blaketolmie/LFR/LFR Report LaTeX - Sections split up/JSON/example error  “LaTeX Workshop” and “vscode-pdf” clash.png

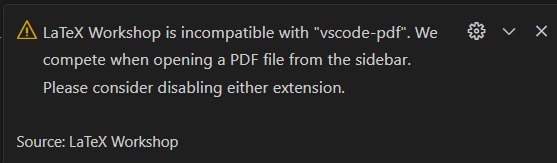
LFR Report LaTeX - Sections split up/JSON/example error “LaTeX Workshop” and “vscode-pdf” clash.png
