blaketolmie/LFR/LFR Report LaTeX - Sections split up/JSON/move pdf into new window.png

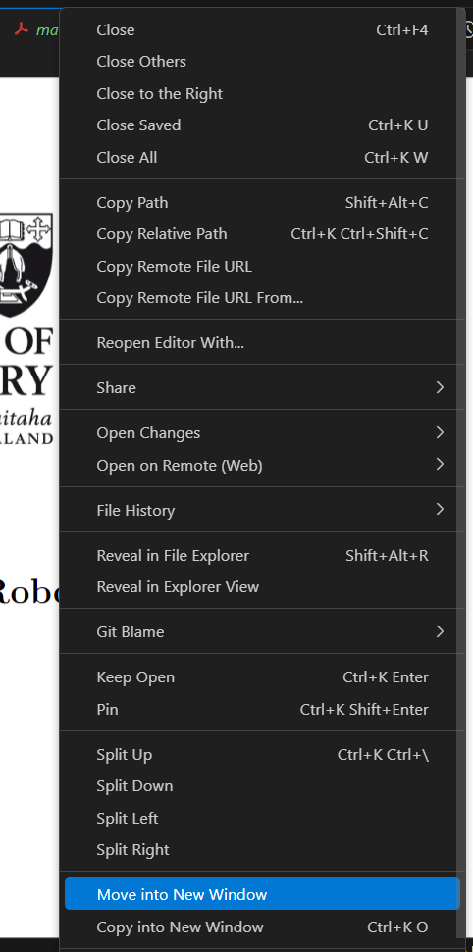
LFR Report LaTeX - Sections split up/JSON/move pdf into new window.png
