blaketolmie/LFR/LFR Report LaTeX - Sections split up/JSON/Opening JSON ctrl and ,  .png

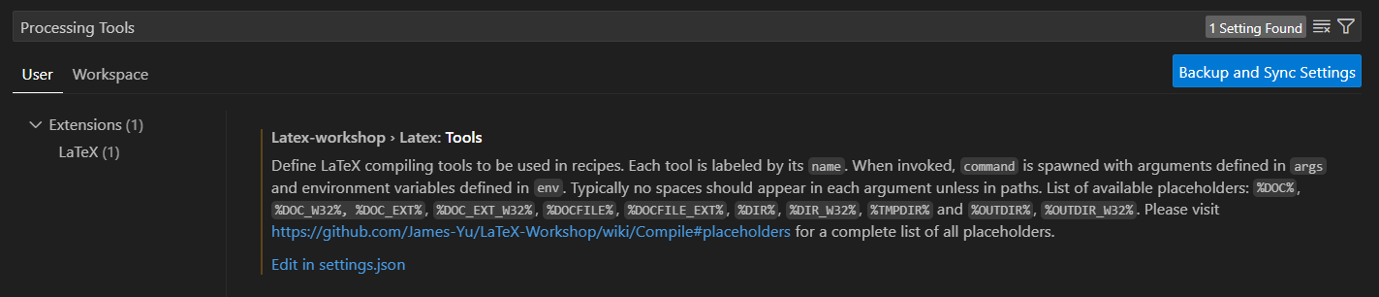
LFR Report LaTeX - Sections split up/JSON/Opening JSON ctrl and , .png
