blaketolmie/LFR/LFR Report LaTeX - Sections split up/REPORT/TrialChart.png

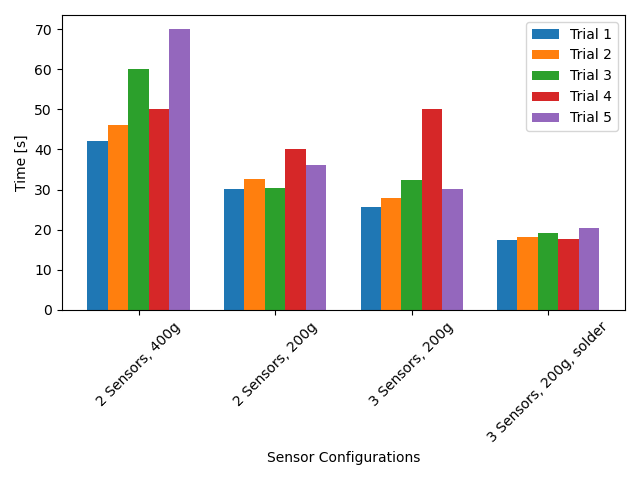
LFR Report LaTeX - Sections split up/REPORT/TrialChart.png
