blaketolmie/LFR/LFR Report LaTeX - Sections split up/REPORT/UCBlack.webp

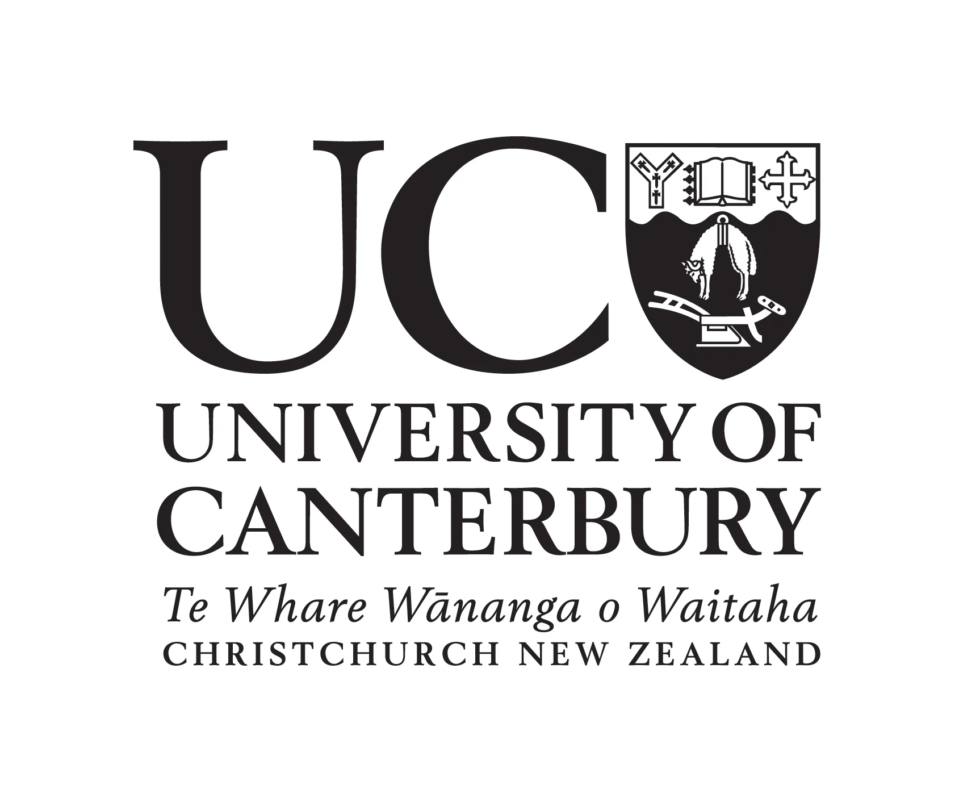
LFR Report LaTeX - Sections split up/REPORT/UCBlack.webp
