blaketolmie/LFR/Reactive Control/LEDs.cpp

#include "LEDs.h"

// Initialize LED pins
void initStatLEDs() {
    pinMode(LED_1, OUTPUT);
    pinMode(LED_2, OUTPUT);
    pinMode(LED_3, OUTPUT);
}

// Turn on specified LED
void turnOnLED(int ledNumber) {
    digitalWrite(ledNumber, HIGH); 
}

// Turn off specified LED
void turnOffLED(int ledNumber) {
    digitalWrite(ledNumber, LOW);
}

// Blink the LED
void blinkLED(int ledNumber, int interval) {
    interval = interval * 1000;
    digitalWrite(ledNumber, HIGH);
    delay(interval);
    digitalWrite(ledNumber, LOW);
    delay(interval);
}
